strawlab/triggerbox/hardware_v1/circuit_board/triggerbox.sch

## KiCad design hardware_v1/circuit_board/triggerbox.sch (2013-12-01, an earlier design)

Schematic: triggerbox.sch

Parts:
D1: LED
P1, P2, P3, P4, P5, P6, P7, P8, P9, P10: BNC
R1: 220
U1: MCP4822
U2: ARDUINO_NANO
U3: SN74HC125

Notes on the sheet:
Analog output
Analog input
Camera triggers
